vives-project-xp/BrakeNBlink/Documentatie/Voorstellingen/Finale Voorstelling/Foto's/ACT-PH-LIGHTSTRIPS-5M-RGB-TW-IC-RTP.webp

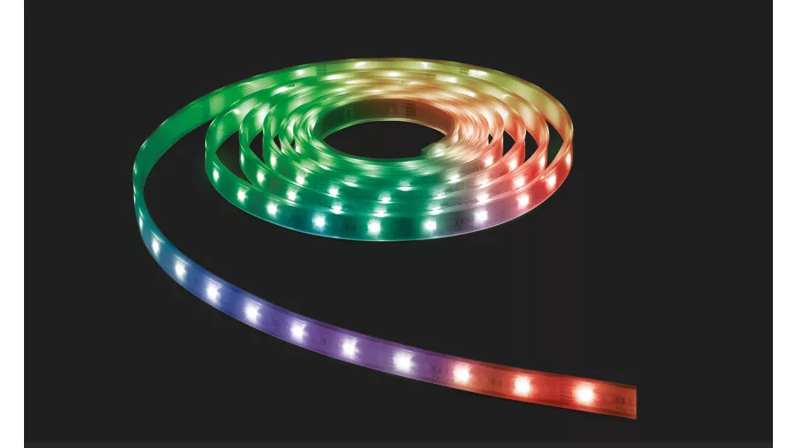
Documentatie/Voorstellingen/Finale Voorstelling/Foto's/ACT-PH-LIGHTSTRIPS-5M-RGB-TW-IC-RTP.webp
