vives-project-xp/BrakeNBlink/Documentatie/Voorstellingen/Finale Voorstelling/Foto's/cyclist-woman-broken-bike-isolated-illustration-weeping-cyclist-woman-standing-near-broken-bike-covered-face-hands-128162111.webp

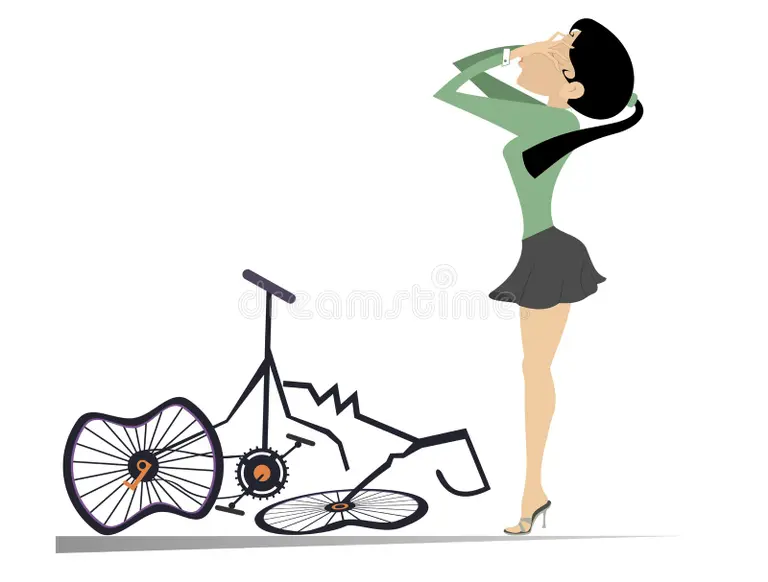
Documentatie/Voorstellingen/Finale Voorstelling/Foto's/cyclist-woman-broken-bike-isolated-illustration-weeping-cyclist-woman-standing-near-broken-bike-covered-face-hands-128162111.webp
