vives-project-xp/BrakeNBlink/Prototypes and simulations/Eindresultaat/LED Strips/Prototype Strips.png

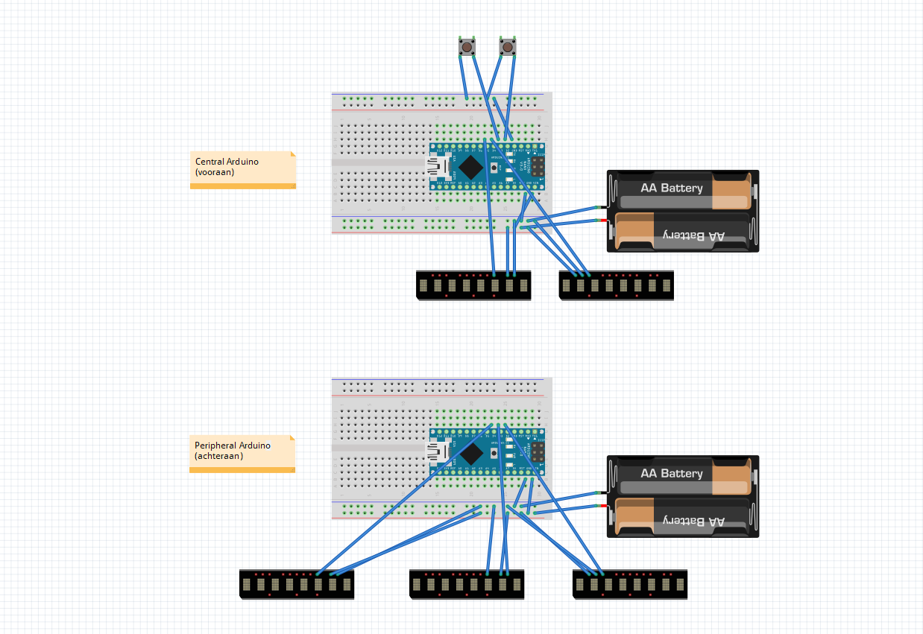
Prototypes and simulations/Eindresultaat/LED Strips/Prototype Strips.png
