vives-project-xp/BrakeNBlink/Prototypes and simulations/Eindresultaat/Normale LEDs/Central.png

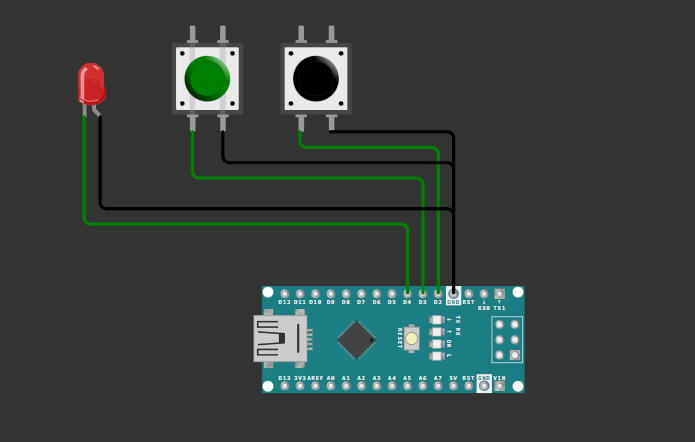
Prototypes and simulations/Eindresultaat/Normale LEDs/Central.png
