vives-project-xp/BrakeNBlink/Prototypes and simulations/Eindresultaat/Normale LEDs/Peripheral.png

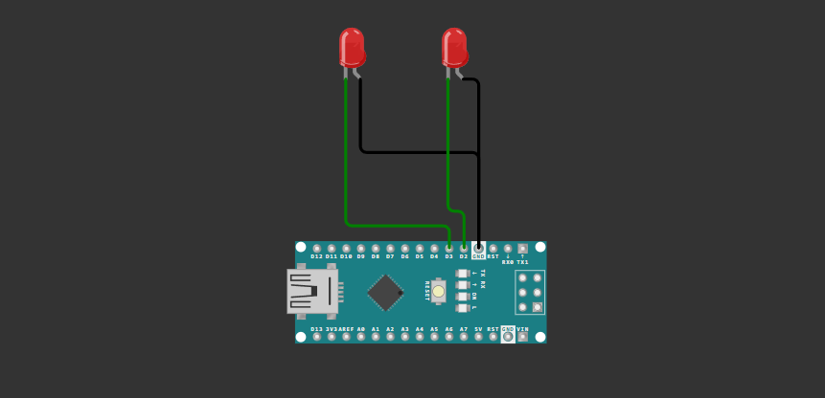
Prototypes and simulations/Eindresultaat/Normale LEDs/Peripheral.png
