vives-project-xp/BrakeNBlink/Prototypes and simulations/Top Down Schema's/Prototypes/TDS eerste prototype/TDS 04-03-2026.png

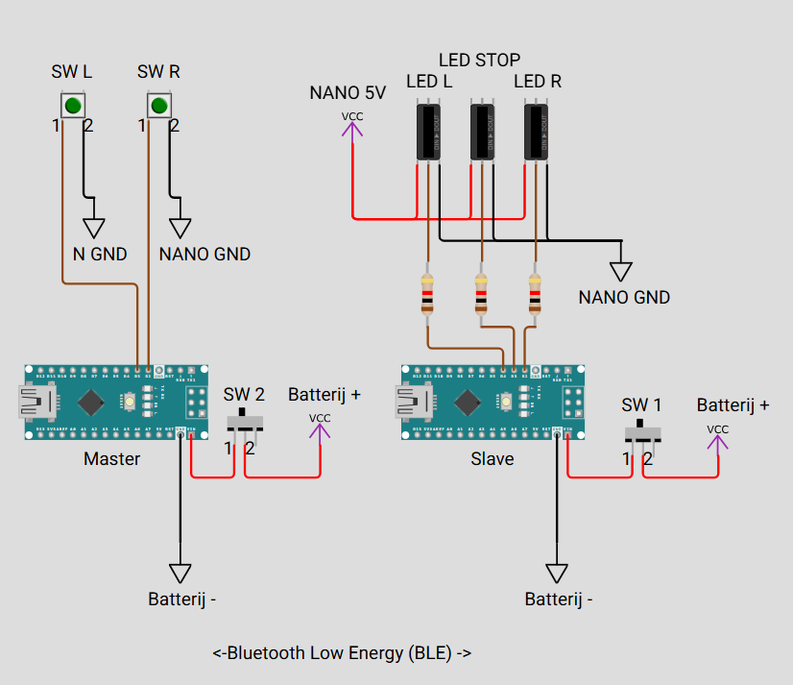
Prototypes and simulations/Top Down Schema's/Prototypes/TDS eerste prototype/TDS 04-03-2026.png
