vives-project-xp/BrakeNBlink/Prototypes and simulations/Top Down Schema's/TDS Master/TDS Master - PP .png

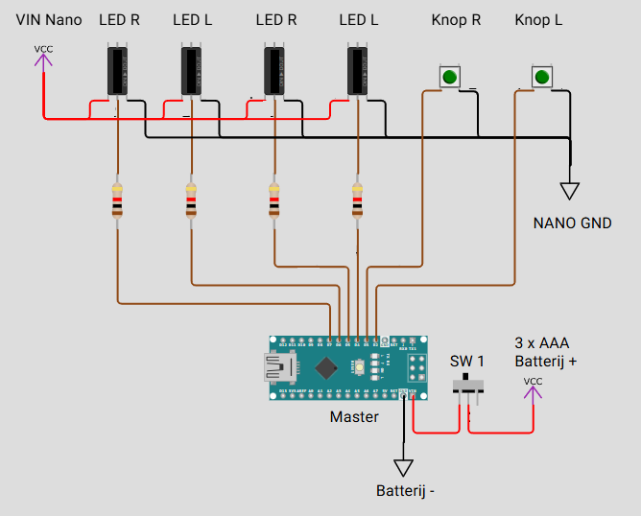
Prototypes and simulations/Top Down Schema's/TDS Master/TDS Master - PP .png
