vives-project-xp/BrakeNBlink/Sociale media/Eerste prototype op de fiets/WhatsApp Image 2026-03-19 at 10.37.07.jpeg

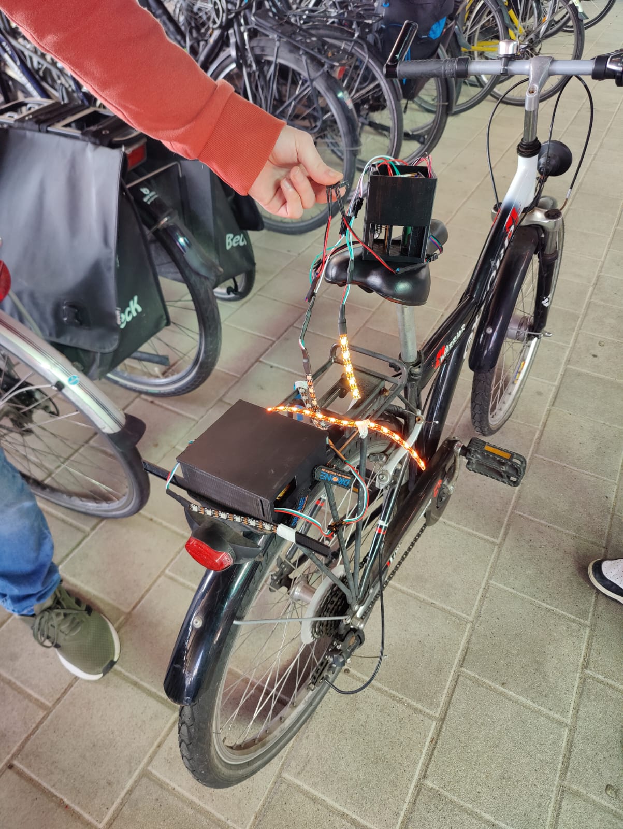
Sociale media/Eerste prototype op de fiets/WhatsApp Image 2026-03-19 at 10.37.07.jpeg
