vives-project-xp/BrakeNBlink/Sociale media/Social media opnames 07-5-2026/WhatsApp Image 2026-05-07 at 10.18.30.jpeg

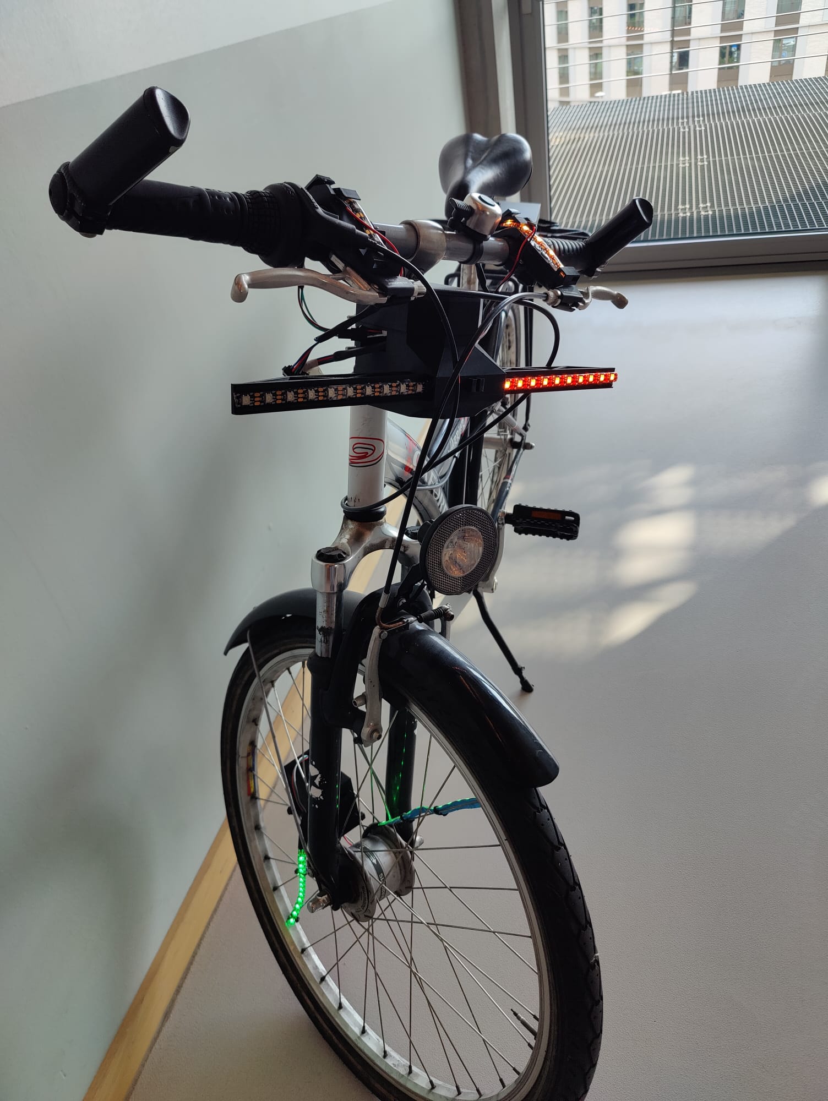
Sociale media/Social media opnames 07-5-2026/WhatsApp Image 2026-05-07 at 10.18.30.jpeg
