vives-project-xp/BrakeNBlink/3D model behuizing/3D Print Files/Voorkant/voorkant_key.stl

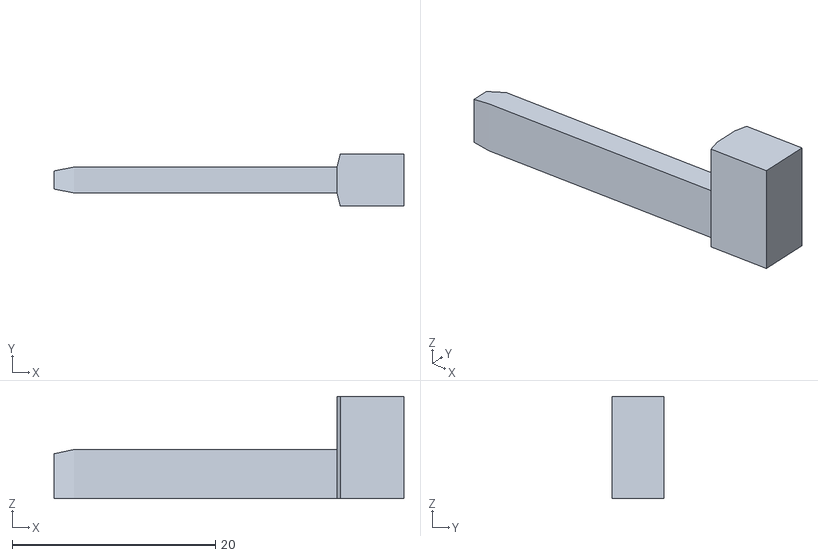
[picture p51: CAD file, 2026-04-22]
3D model behuizing/3D Print Files/Voorkant/voorkant_key.stl
34.4 x 5.16 x 10.1
