vives-project-xp/BrakeNBlink/3D model behuizing/Uitbreiding/Doos_uitbreiding.stl

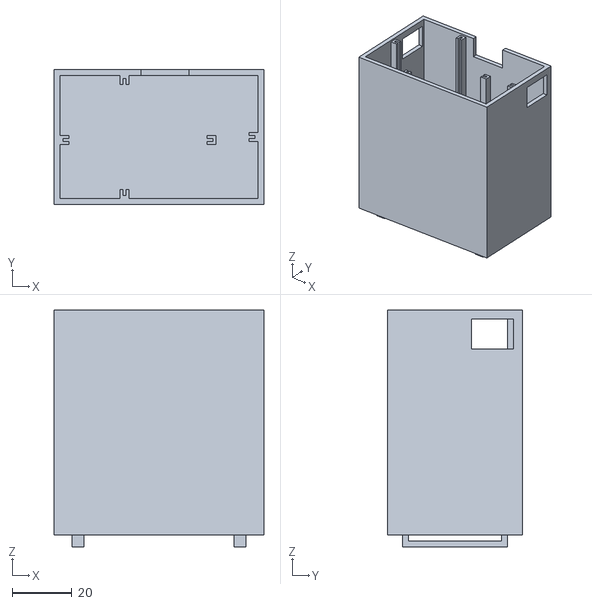
[picture p52: CAD file, 2026-04-23]
3D model behuizing/Uitbreiding/Doos_uitbreiding.stl
70.0 x 45.0 x 79.0
