vives-project-xp/BrakeNBlink/Sociale media/Led's solderen/WhatsApp Image 2026-03-19 at 10.39.36 (1).jpeg

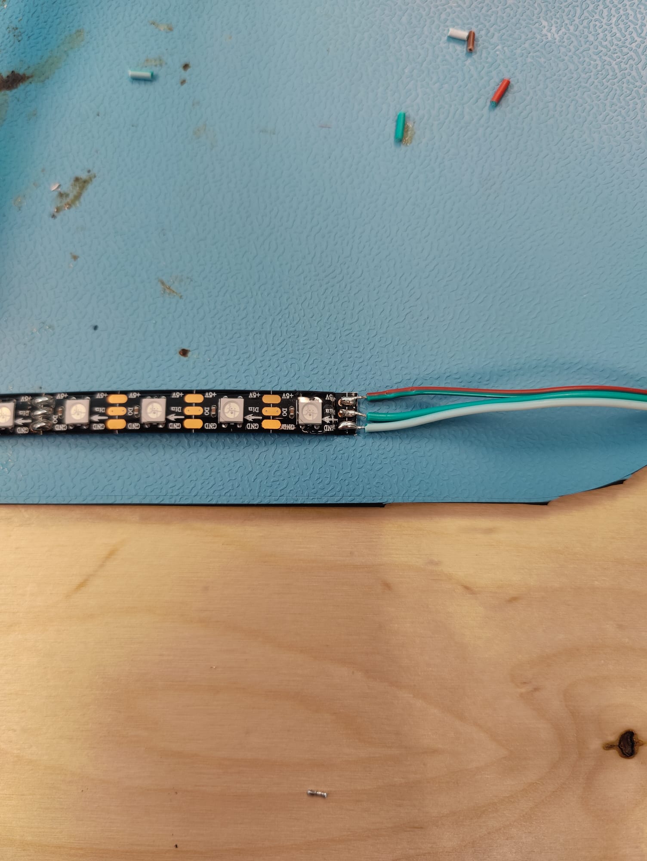
Sociale media/Led's solderen/WhatsApp Image 2026-03-19 at 10.39.36 (1).jpeg
