vives-project-xp/BrakeNBlink/Prototypes and simulations/Led strip Test/Schermafbeelding 2026-03-05 144328.png

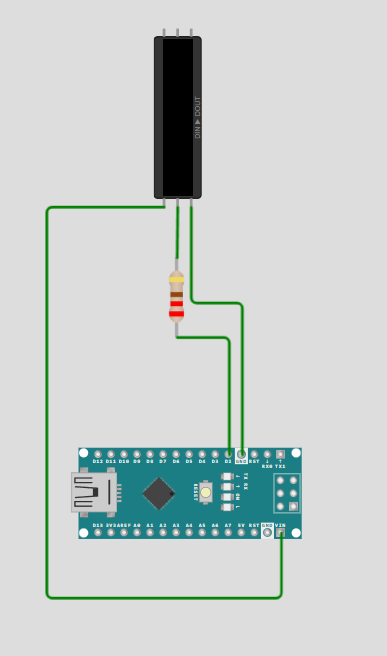
Prototypes and simulations/Led strip Test/Schermafbeelding 2026-03-05 144328.png
