vives-project-xp/BrakeNBlink/Prototypes and simulations/Led strip Test/WhatsApp Image 2026-03-05 at 14.45.18.jpeg

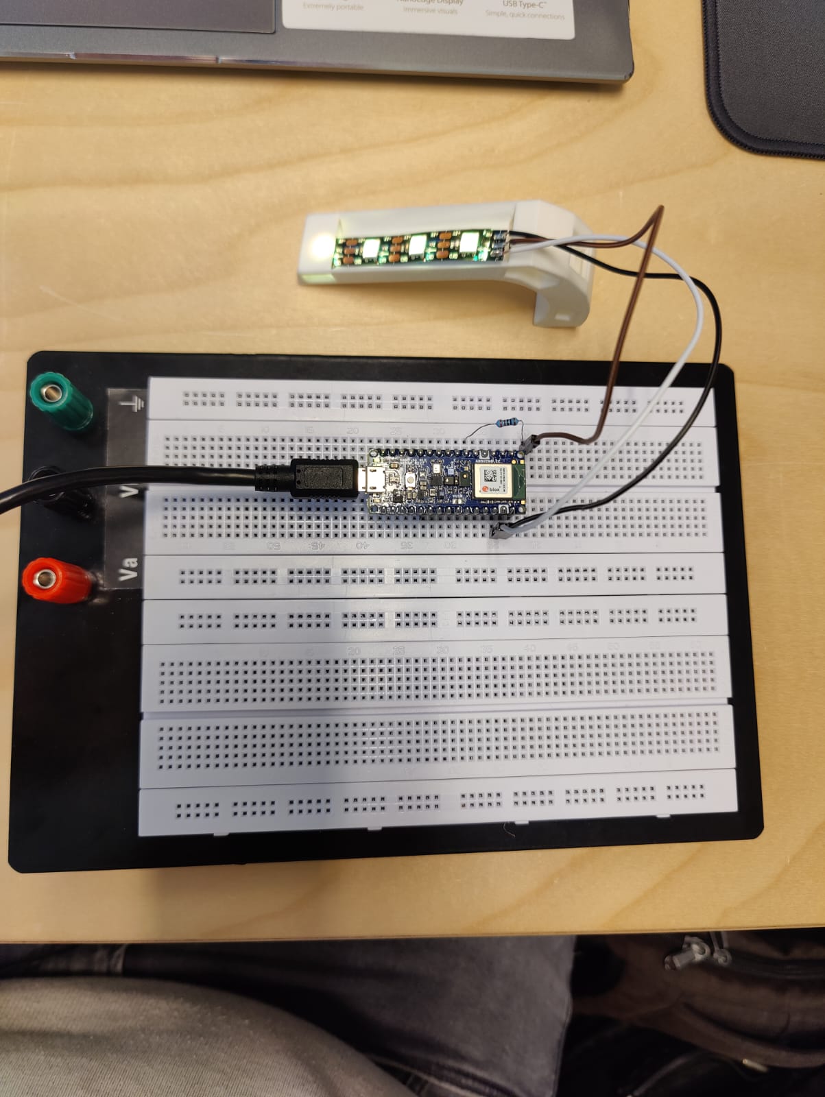
Prototypes and simulations/Led strip Test/WhatsApp Image 2026-03-05 at 14.45.18.jpeg
