vives-project-xp/BrakeNBlink/Prototypes and simulations/Eerste versie op breadboard/1000003255.jpg

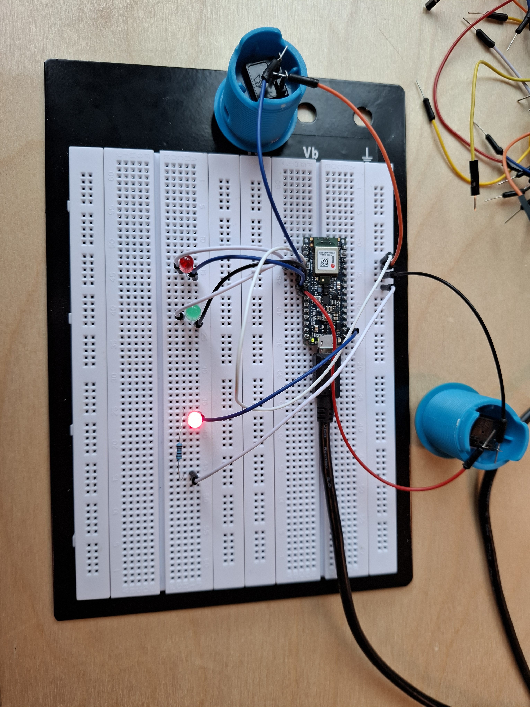
Prototypes and simulations/Eerste versie op breadboard/1000003255.jpg
