vives-project-xp/BrakeNBlink/Prototypes and simulations/Eindresultaat/Normale LEDs/1000003256.jpg

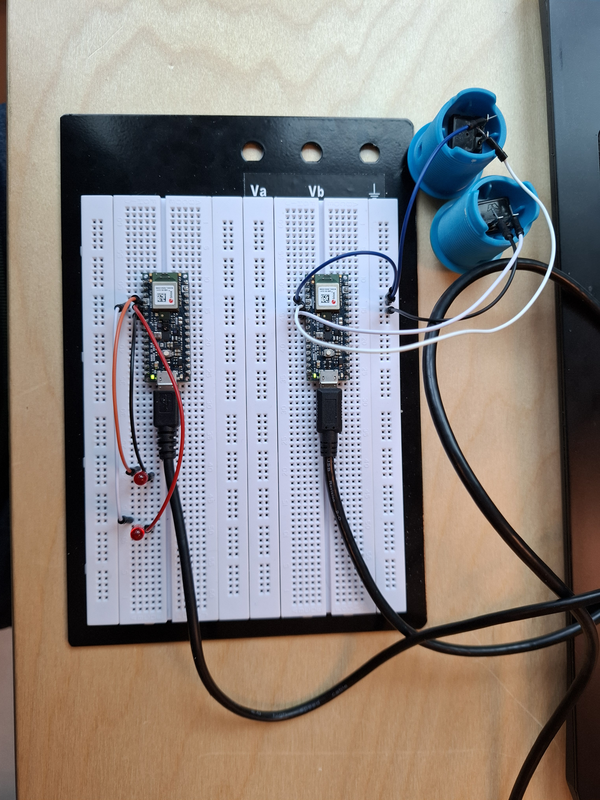
Prototypes and simulations/Eindresultaat/Normale LEDs/1000003256.jpg
