vives-project-xp/BrakeNBlink/Prototypes and simulations/Eindresultaat/Normale LEDs/1000003314.jpg

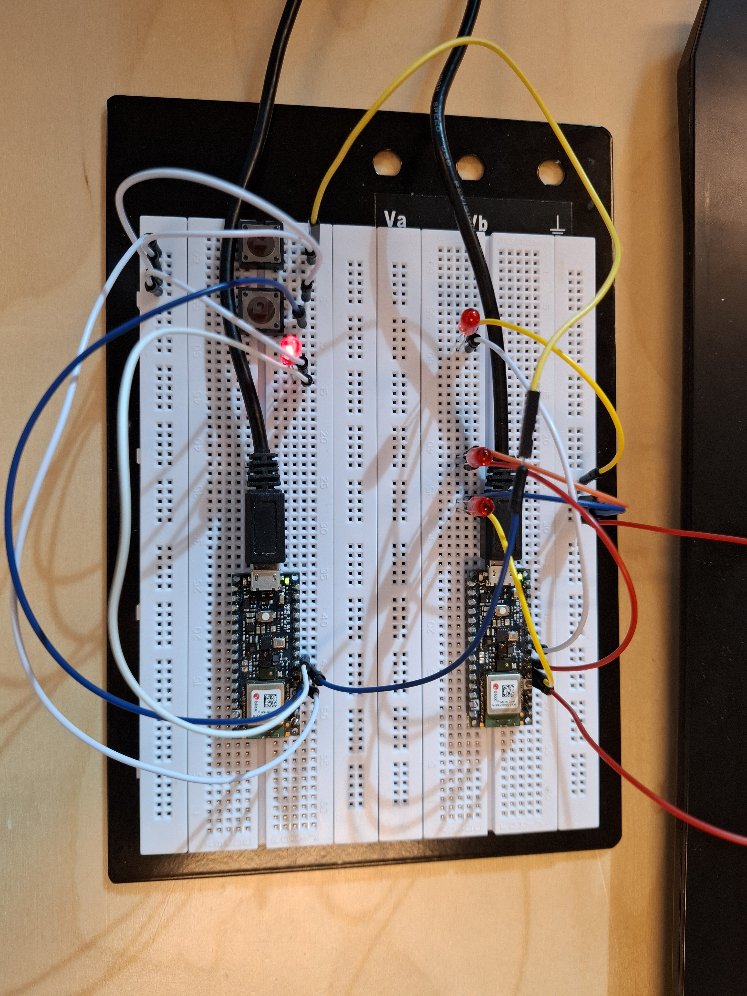
Prototypes and simulations/Eindresultaat/Normale LEDs/1000003314.jpg
